Fasstoch/My-Hexapod-Build/Bearings.JPG

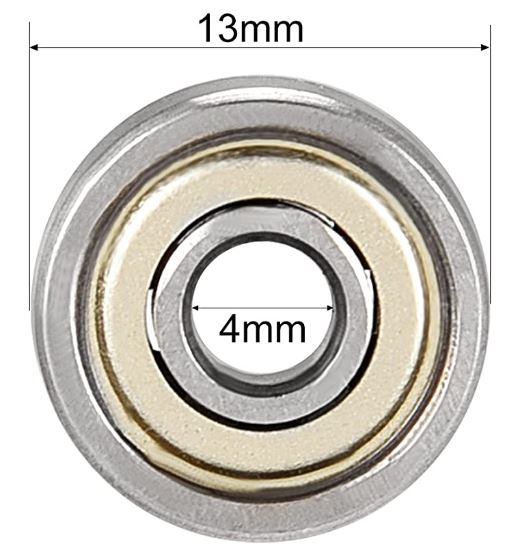
Bearings.JPG
