Fasstoch/My-Hexapod-Build/Images/Body bottom.JPG

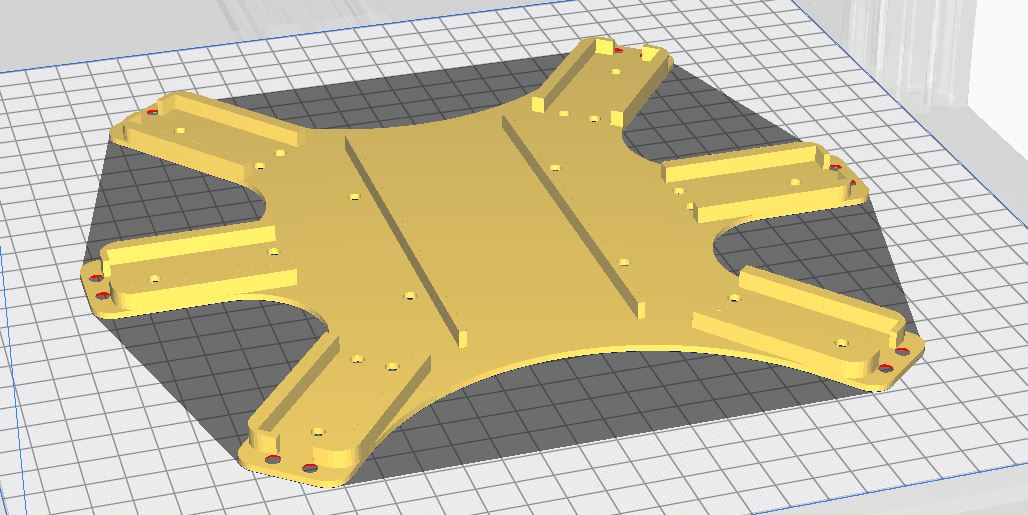
Images/Body bottom.JPG
