Fasstoch/My-Hexapod-Build/Images/Body Top.JPG

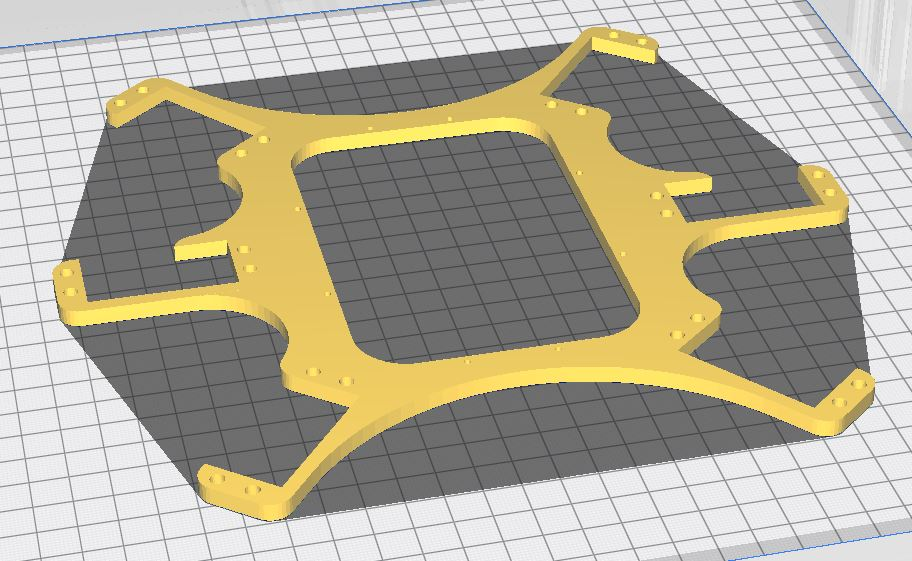
Images/Body Top.JPG
