Fasstoch/My-Hexapod-Build/Images/IMG_9647.JPEG

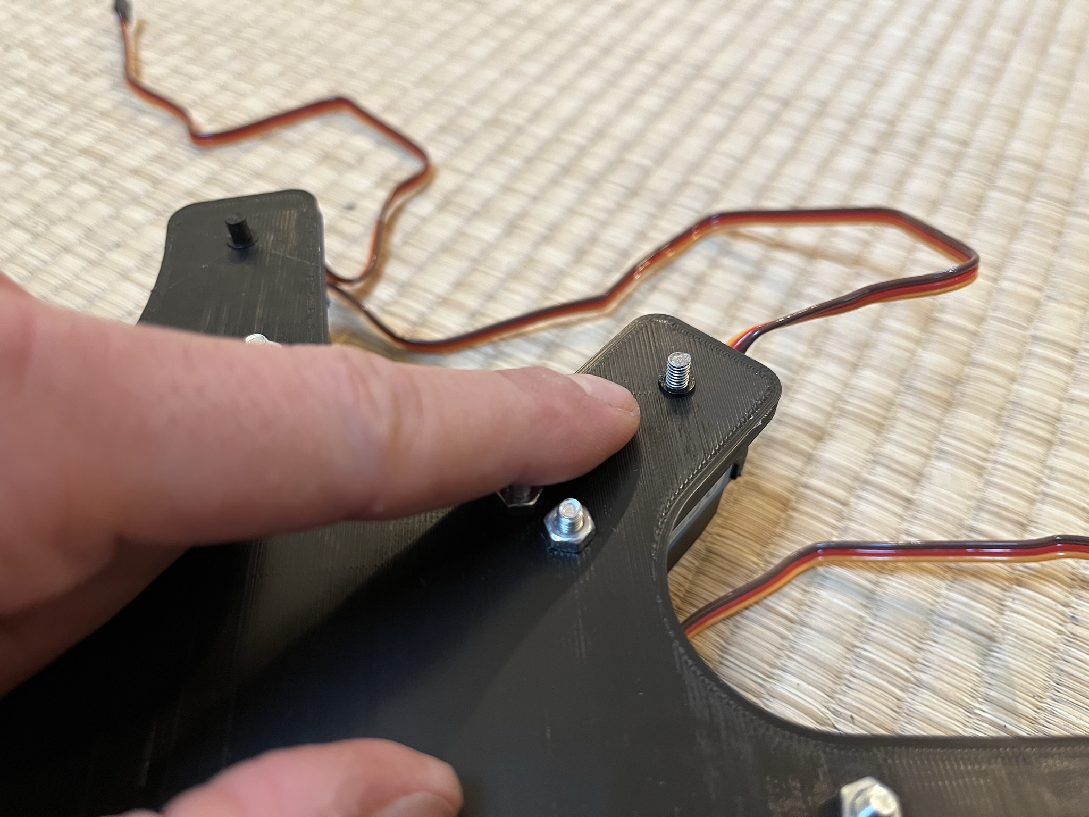
Images/IMG_9647.JPEG
