Fasstoch/My-Hexapod-Build/Images/Spacer.JPG

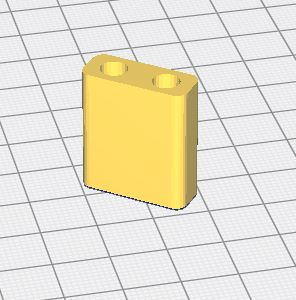
Images/Spacer.JPG
