Fasstoch/My-Hexapod-Build/Images/Support elec.JPG

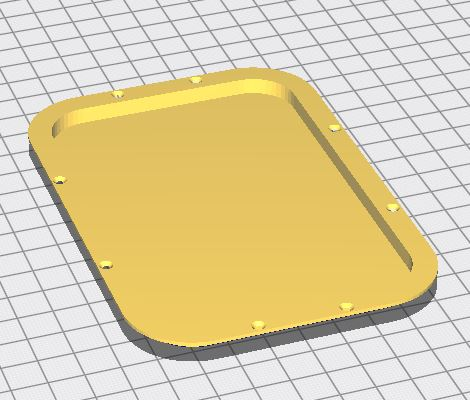
Images/Support elec.JPG
