Fasstoch/My-Hexapod-Build/Images/Tibia.JPG

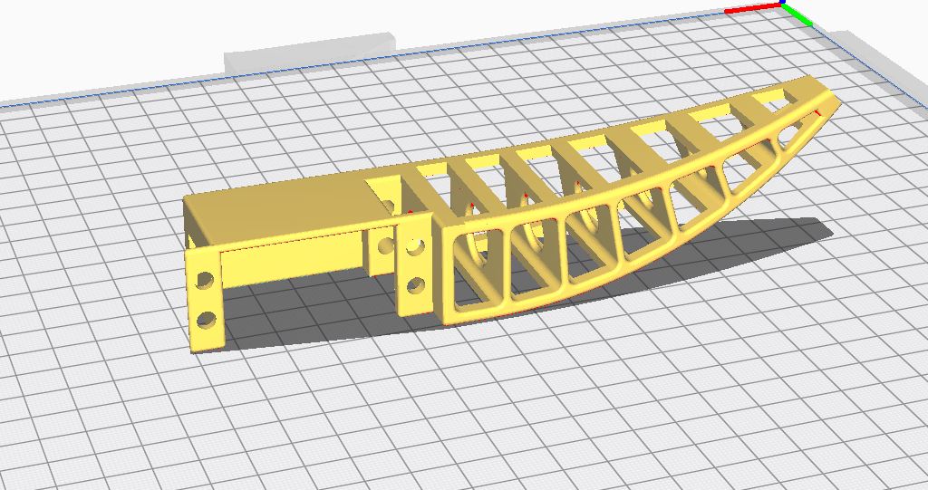
Images/Tibia.JPG
