Fasstoch/My-Hexapod-Build/Servo_dimensions.JPG

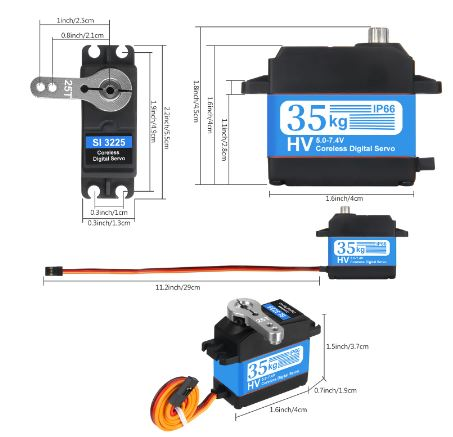
Servo_dimensions.JPG
