Fasstoch/My-Hexapod-Build/Code/Work/Hexapod_avecTx_Modulaire/Angles.cpp

#include "Angles.h"


// Define servos Init and Target positions
int initAngles[3] = {90,10,20}; 
int targetAngles[3] = {90,60,120};

int currentAngles[3] = {90,10,20};  // Initialisation de la variable
